AmirDavoodi/SimulatorWeatherLamp/Arduino_Code_0.23/LED_three_color_rotating/LED_three_color_rotating.ino

// NeoPixel Ring simple sketch (c) 2013 Shae Erisson
// released under the GPLv3 license to match the rest of the AdaFruit NeoPixel library

#include <Adafruit_NeoPixel.h>
#ifdef __AVR__
  #include <avr/power.h>
#endif

// Which pin on the Arduino is connected to the NeoPixels?
// On a Trinket or Gemma we suggest changing this to 1
#define PIN            D2

// How many NeoPixels are attached to the Arduino?
#define NUMPIXELS      60

// When we setup the NeoPixel library, we tell it how many pixels, and which pin to use to send signals.
// Note that for older NeoPixel strips you might need to change the third parameter--see the strandtest
// example for more information on possible values.
Adafruit_NeoPixel pixels = Adafruit_NeoPixel(NUMPIXELS, PIN, NEO_GRB + NEO_KHZ800);

int delayval = 500; // delay for half a second

void setup() {
  // This is for Trinket 5V 16MHz, you can remove these three lines if you are not using a Trinket
#if defined (__AVR_ATtiny85__)
  if (F_CPU == 16000000) clock_prescale_set(clock_div_1);
#endif
  // End of trinket special code

  pixels.begin(); // This initializes the NeoPixel library.
}

void set_LED_color(int i, int color_mode, int intensity = 255) {
  if (color_mode == 1){
    pixels.setPixelColor(i, pixels.Color(intensity, 0, 0));
  } else if(color_mode == 2){
    pixels.setPixelColor(i, pixels.Color(0, intensity ,0));
  } else if(color_mode == 3){
    pixels.setPixelColor(i, pixels.Color(0, 0 ,intensity));
  }
}


void loop() {

  // For a set of NeoPixels the first NeoPixel is 0, second is 1, all the way up to the count of pixels minus one.
  int i =0;
  int intensity = 255;
  while( true ) {
      int color_mode = 1;
      if (i % 20){
        if (color_mode == 1){
          color_mode = 2;
        } else if(color_mode == 2){
          color_mode = 3;
        } else if(color_mode == 3){
          color_mode = 1;
        }
      }

      // set the color of led
      set_LED_color(i, color_mode, intensity);
      
      delay(delayval); // Delay for a period of time (in milliseconds).
      pixels.show(); // This sends the updated pixel color to the hardware.
      i++;
      if(i == 60){
        i = 0;
      }
  }
  for(int i=0;i<NUMPIXELS;i++){

    
    

    

    

  }
}
