AmirDavoodi/SimulatorWeatherLamp/Arduino_Code_0.23/combined_api_led_touchsensors/icons.h

const uint8_t activeSymbol[] PROGMEM = {
    B00000000,
    B00000000,
    B00011000,
    B00100100,
    B01000010,
    B01000010,
    B00100100,
    B00011000
};

const uint8_t inactiveSymbol[] PROGMEM = {
    B00000000,
    B00000000,
    B00000000,
    B00000000,
    B00011000,
    B00011000,
    B00000000,
    B00000000
};
